KaisLissera/IR-motion-sensor/Doc/МГТУ.469335.001 Узел печатный.pdf

Формат
Кол.
А3 | | МГТУ.469335.001 СБ | Сборочный чертёж
А2 | | МГТУ.469335.001 Э3 | Схема электрическая
| | | | | принципиальная
| А4 | | | МГТУ.469335.001 ПЭ3 | Перечень элементов
| * | | | МГТУ.758741.001 ДЗЗ | Данные проектирования | *)CD
А3 | 1
Изм. | Лист | № докум. | Подп. | Дата
| | Разраб. | | | Спецификация | Лит. | Лист | Листов
Пров. | | | | | | | | 5

# МГТУ.469335.001

Подп. и дата Взам. инв. №

Инв. № подл.
МГТУ им Н.Э. Баумана
кафедра РЛ1

Н. контр.
Утв. | Круглов

### 1 Узел печатный

Краснинский Поз.

Инв. № дубл. Подп. дата

Документация

Детали

Плата печатная

МГТУ.758741.001

| Конденсаторы
2 | 04025U1CAT2A | 1 | С21*
| 1пФ+-0,25пФ 50В NP0
3 | 04025U5R6CAT2A | 1 | С20*
| | | 5,6пФ+-0,25пФ 50В NP0
| 4 | | 06032U18CAT2A | 4 | С23-С26
| | | 18пФ+-0,25пФ 200В NP0
| | | AVX Corporation
| 5 | | К10-90-1608-50В-100пФ+-5%-МП0 | 1 | С19
| 6 | | К10-90-1608-10В-100нФ+-10%-Н30 | 13 | C1-C5,C8-C15
| 7 | | К10-90-1608-10В-10мкФ+-10%-Н30 3 | | C16-C18
| | | ШУКР.673511.002 ТУ

Зона
Обозначение

Наименование

1

Примечание

Прочие изделия

Перв. примен.

МГТУ.464415.001

Справ. №

Копировал
Формат А4

| Микросхемы
8 | MCP1700T-3300E/TT | 1 | DA1
| Microchip Technology
9 | STM32F072RBT6 | 1 | DD1
| STMicroelectronics
| Предохранители
10 | MF-MSMF050 0,5А, Bourns | 1 | F1
| Приборы звуковой
| сигнализации
11 | HC0905A, JL World | 1 | HA1
| Индуктивности
13 | КИК 1005-1,2 нГн +-5% О-Л | 1 | L1*
| РКМУ.671340.002 ТУ
14 | BLM18AG102SN1D, Murata | 2 | L2,L3
| Резисторы
15 | Р1-8В-0,1-1 кОм+-10% Л-П-М | 6 | R9-R14
16 | Р1-8В-0,1-5,1 кОм+-10% Л-П-М | 2 | R1,R2
17 | Р1-8В-0,1-10 кОм+-10% Л-П-М | 1 | R3
18 | Р1-8В-0,1-100 кОм+-10% Л-П-М | 2 | R6,R7
| ОЖО.467.164 ТУ
Подп. | Дата

Приме-

Лист

# МГТУ.469335.001 2

№ докум.

Обозначение

| Светодиоды
12 | SMD05050C6 | 1 | HL1

Поз.

Инв. № подл.

Изм. Лист

Подп. и дата Взам. инв. № Инв. № дубл. Подп. дата

| Выключатели кнопочные
19 | KLS7-P8.5x8.5-1 | 1 | SB1
| Модуляторы
20 | RFM95W 868МГц, Hope RF | 1 | U1
| Диоды
21 | BAT760, NXP | 1 | VD2
22 | USBLC6-2SC6, STMicroelectronics | 1 | VD1
| Транзисторы
23 | SI2302A, UMW | 2 | VT1, VT3
| Резонаторы кварцевые
29 | 12MHz SMD03225C4 | 1 | ZQ1
30 | 32.768kHz SMD03215C2 | 1 | ZQ2
Переменные данные | для исполнений
| МГТУ.464415.001-00

Прочие изделия

| Резисторы
31 | Р1-8В-0,1-0 Ом+-10% Л-П-М | 1 | R17
Обозначение | Приме-
| Разъёмы
24 | PLS-2R тип D, Connfly | 1 | XP1
25 | PLS-6R тип D, Connfly | 1 | XP2
26 | USB Type-C 213716-0001, Ruichi | 1 | XS1

Инв. № дубл.

Подп. дата

Инв. № подл.

Лист | № докум.

Взам. инв. №

Подп. и дата

МГТУ.469335.001 | Лист 3 Изм.

Переменные данные | для исполнений
| МГТУ.464415.001-01

Прочие изделия

| Фотоэлементы
32 | SFH213FA, Osram | 1 | BL1
33 | TSOP4836, Vishay | 1 | BL2
| Конденсаторы
2 | 04025U1CAT2A 1пФ+-0,25пФ | 1 | C27*
| 50В NP0, AVX Corporation
34 | К10-90-1608-6,3В-680пФ+-10%-Н3 1 | | C22
6 | К10-90-1608-10В-100нФ+-10%-Н30 2 | | C6,C7
| ШУКР.673511.002 ТУ
| Микросхемы
35 | MCP6001RT-I/OT | 1 | DA1
| Microchip Technology

Резисторы
36 | Р1-8В-0,1-100 Ом+-10% Л-П-М | 1 | R4,R5
15 | Р1-8В-0,1-1 кОм+-10% Л-П-М | 1 | R8
18 | Р1-8В-0,1-100 кОм+-10% Л-П-М | 2 | R15
| ОЖО.467.164 ТУ
| Выключатели кнопочные
37 | KLS7-TS6601-5.0-180 | 1 | SB2
| KLS Electronics

Инв. № дубл. Подп. дата

Инв. № подл.

Взам. инв. №

Подп. и дата

МГТУ.469335.001 | Лист
Изм. | 4

| Диоды
38 | ESDA5V3L, STMicroelectronics | 1 | VD3

МГТУ.464415.001-02

Прочие изделия

| Резисторы
39 | Р1-8В-0,1-10 Ом+-10% Л-П-М | 1 | R16
| ОЖО.467.164 ТУ
| Выключатели кнопочные
37 | KLS7-TS6601-5.0-180 | 1 | SB2
| KLS Electronics
| Диоды
38 | ESDA5V3L, STMicroelectronics | 1 | VD3
40 | TSAL6200, Vishay | 1 | VD4
| Транзисторы
23 | SI2302A, UMV | 1 | VT2

Инв. № дубл. Подп. дата Инв. № подл.

Взам. инв. № Подп. и дата

# МГТУ.469335.001 Лист

5 Изм.
