KaisLissera/IR-motion-sensor/Doc/МГТУ.469335.001 Э3 Система электронного хронометража.pdf

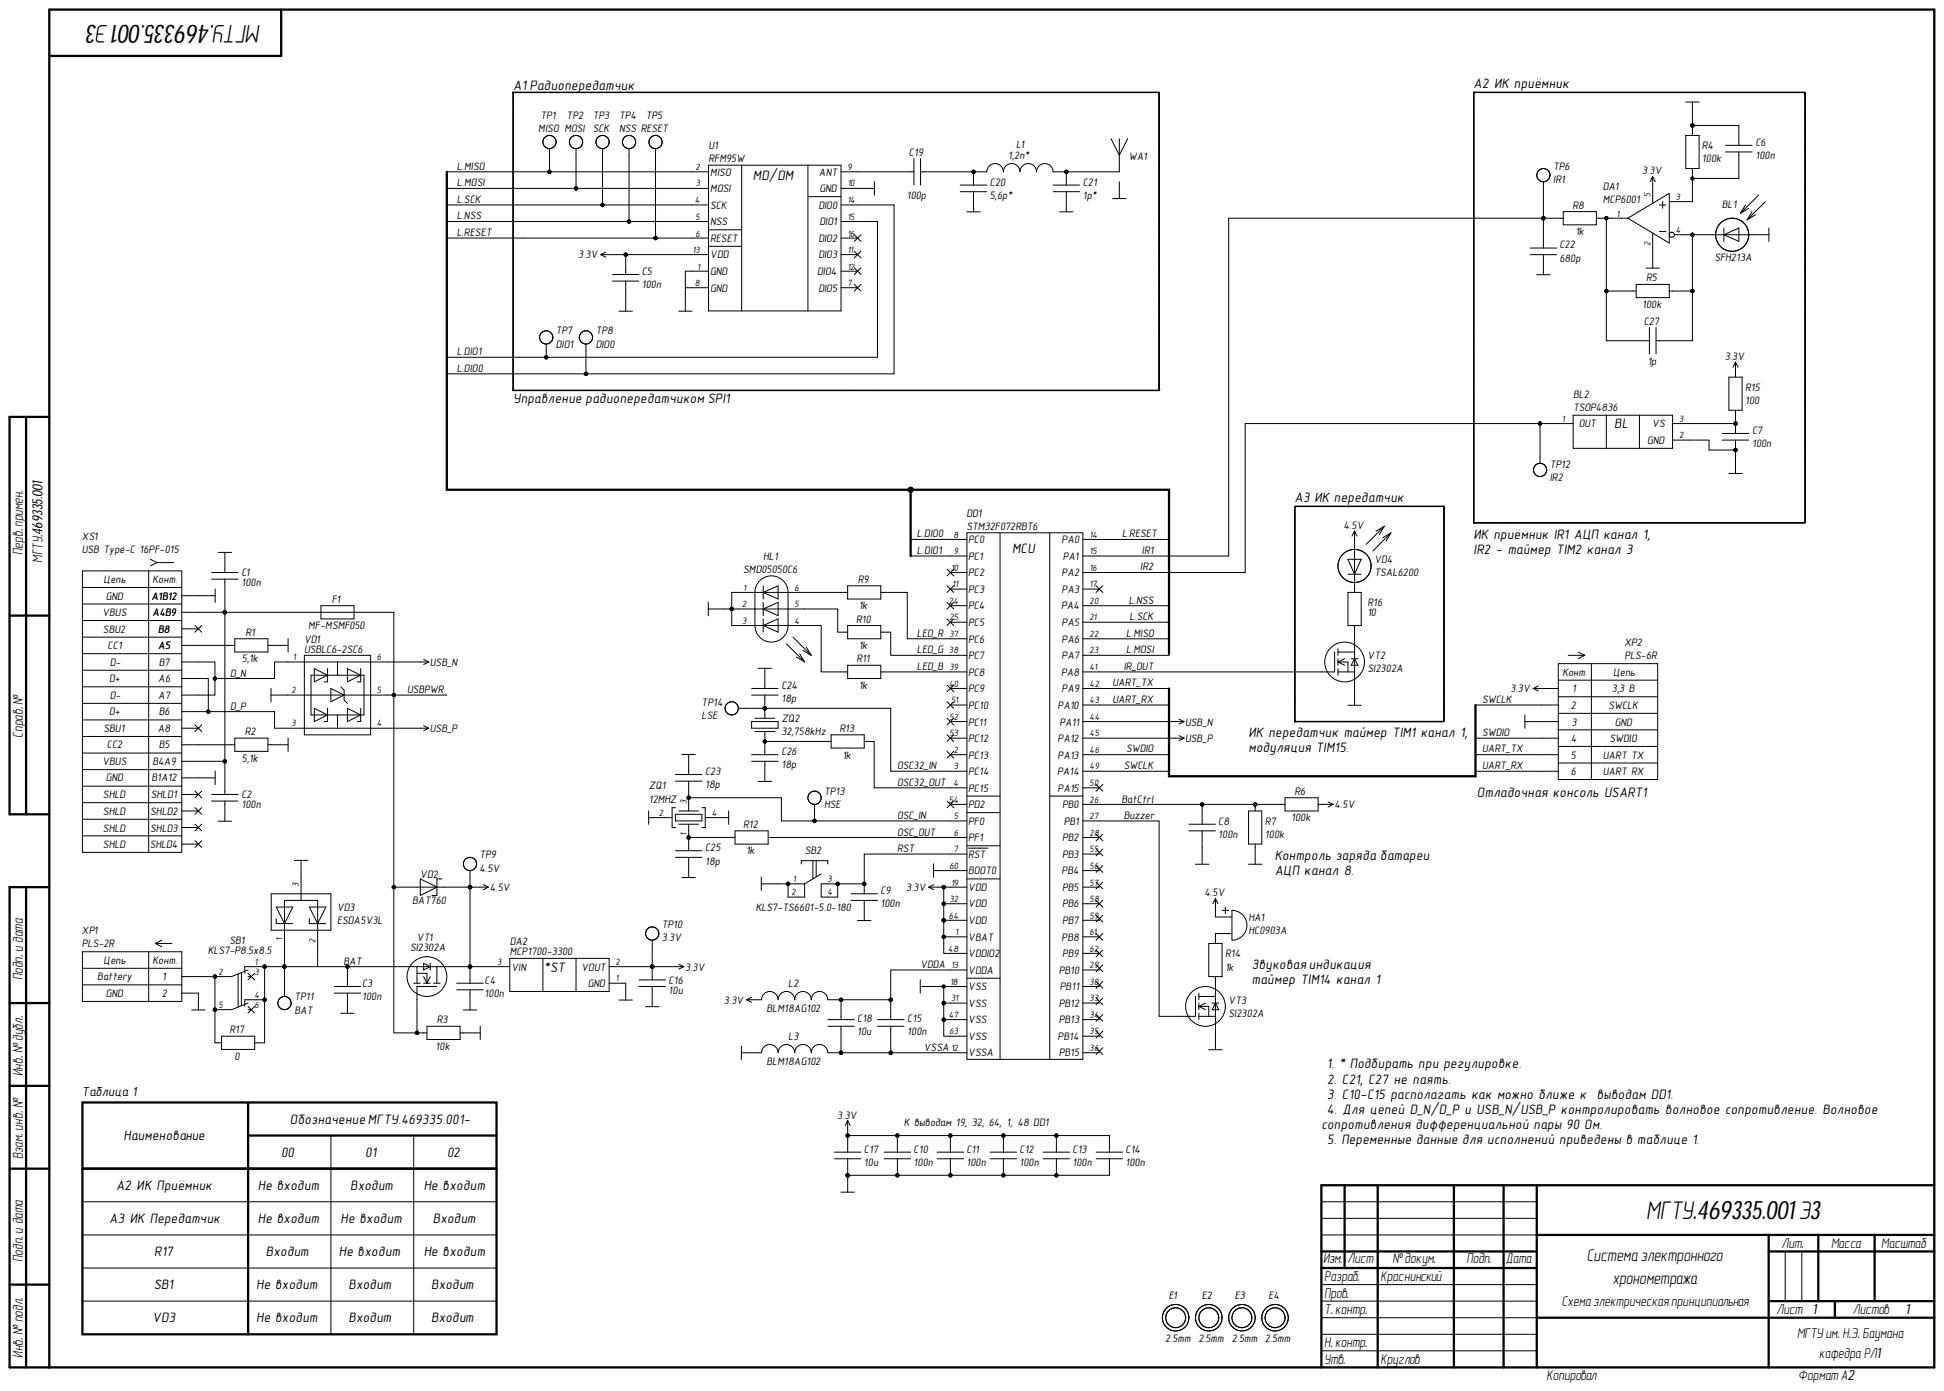
[picture p32: page 1]

L.MOSI | MOSI 3 | MD/DM

L.SCK | SCK 4

Инв. № подл. Подп. и дата Инв. №дубл. Подп. и дата Взам. инв. № Перв.примен. Справ. №

А3 ИК передатчик 4.5V

ИК приёмник IR1 АЦП канал 1,
IR2 - таймер TIM2 канал 3

ИК передатчик таймер TIM1 канал 1,
модуляция TIM15.

1. * Подбирать при регулировке.
2. C21, C27 не паять.
3. C10-C15 располагать как можно ближе к выводам DD1.
4. Для цепей D_N/D_P и USB_N/USB_P контролировать волновое сопротивление. Волновое
сопротивления дифференциальной пары 90 Ом.
5. Переменные данные для исполнений приведены в таблице 1.

Наименование | Обозначение МГТУ.469335.001-

А2 ИК Приёмник | Не входит | Входит | Не входит

МГТУ.469335.001 Э3

А3 ИК Передатчик | Не входит | Не входит | Входит

Н.контр.
Утв. | Круглов

МГТУ им. Н.Э. Баумана кафедра РЛ1
