KaisLissera/IR-motion-sensor/Bagryanets_hw/Photodiod_Amplifier.cir

[Main]
FileType=CIR
Version=12.00
Program=Micro-Cap
Component Version=10.00
Shape Version=11.00
Screen=1920,1080
MCAPVersion=12.2.0.5
Key ID=Demo
NLCnt=48
TXCnt=10

[shapedef]
Name=Battery
Line=0,0,22,0
Line=22,-3,22,3
Line=26,-7,26,7
Line=26,0,48,0
Current=32,8,16,8

[shapedef]
Name=Capacitor
Line=0,0,22,0
Line=22,-8,22,8
Line=26,-8,26,8
Line=26,0,48,0
Current=32,12,16,12

[shapedef]
Name=Diode.root
Line=0,0,20,0
Line=28,0,48,0
Rectangle=18,-8,20,8
PolyClosed=3
PolyLine=20,0
PolyLine=28,-8
PolyLine=28,8
Current=32,16,16,16

[shapedef]
Name=Ground
Line=0,0,12,0
Line=12,-8,12,8
Line=18,-4,18,4
Line=24,0,24,0

[shapedef]
Name=Minus.root
Line=-2,0,2,0

[shapedef]
Name=Opamp5
Root="Opamp.root",0,0,0
Root="Plus.root",25,-4,0
Root="Minus.root",25,52,0
Line=32,56,32,34
Line=32,-8,32,13

[shapedef]
Name=Opamp.root
Line=0,48,6,48
Line=0,0,5,0
Line=6,-4,6,52
Line=6,-4,48,24
Line=6,52,48,24
Line=48,24,72,24
Line=10,12,14,12
Line=12,10,12,14
Line=10,36,14,36
Line=4,0,6,0

[shapedef]
Name=Photodiode3
Root="Diode.root",0,48,0
Line=16,22,22,28
Line=10,28,16,34
PolyClosed=3
PolyLine=20,30
PolyLine=24,26
PolyLine=24,30
PolyClosed=3
PolyLine=14,36
PolyLine=18,32
PolyLine=18,36
Ellipse=-2,-2,2,2
FColor=None
Ellipse=46,-2,50,2
FColor=None
Line=8,6,8,10
Line=10,8,6,8

[shapedef]
Name=Plus.root
Line=-2,0,2,0
Line=0,-2,0,2

[shapedef]
Name=Pulse_Source
Root="Vsource.root",0,0,0
Line=20,-4,20,0
Line=20,0,26,0
Line=26,0,26,4

[shapedef]
Name=Resistor
PolyOpen=12
PolyLine=0,0
PolyLine=0,0
PolyLine=12,0
PolyLine=14,-4
PolyLine=18,4
PolyLine=22,-4
PolyLine=26,4
PolyLine=30,-4
PolyLine=34,4
PolyLine=36,0
PolyLine=48,0
PolyLine=48,0
Current=32,8,16,8

[shapedef]
Name=Vsource.root
Line=0,0,12,0
Line=36,0,48,0
Ellipse=12,-12,36,12
FColor=None
Line=7,5,7,9
Root="Plus.root",41,7,0
Current=32,16,16,16

[compdef]
Name=Battery
Definition=Battery
Shape=Battery
Mask=6145
Used=68
memo=Battery
Label Offset=19,7,10,13
PinCnt=2
Pin="Plus",6,0,-4,-5
Pin="Minus",0,0,-10,-5

[compdef]
Name=Ground
Definition=Ground
Shape=Ground
Mask=513
Used=296
memo=Ground
Label Offset=0,0,0,0
PinCnt=1
Pin="PinA",0,0,-3,-7

[compdef]
Name=Resistor
Definition=Resistor
Shape=Resistor
Mask=6145
Used=186
memo=Resistor
Label Offset=18,6,8,11
PinCnt=2
Pin="Plus",6,0,-10,-4
Pin="Minus",0,0,-14,-4

[compdef]
Name=Pulse Source
Definition=Pulse source
Shape=Pulse_Source
Mask=4864
Used=8
memo=Pulse Source
Label Offset=18,13,15,9
PinCnt=2
Pin="Plus",6,0,-5,-4
Pin="Minus",0,0,-19,-4

[compdef]
Name=SFH213
Definition=Subckt
Shape=Photodiode3
Mask=4224
Used=1
memo=PIN Photodiode Vr=20V Ip=135uA Id=1nA
Link=http://catalog.osram-os.com/catalogue/catalogue.do?act=downloadFile&favOid=020000030000b9ee000100b6
Label Offset=16,58,-19,10
PinCnt=4
Pin="OPT_IN+",a,0,0,-22,-4
Pin="OPT_IN-",a,6,0,-22,-4
Pin="CATH",a,0,6,-16,19
Pin="ANO",a,6,6,-7,19
Power=0.15

[compdef]
Name=Capacitor
Definition=Capacitor
Shape=Capacitor
Mask=7425
Used=28
memo=Capacitor
Label Offset=16,12,12,12
PinCnt=2
Pin="Plus",6,0,-3,-5
Pin="Minus",0,0,-14,-5

[compdef]
Name=LMC6001_NS
Definition=Subckt
Shape=Opamp5
Mask=4224
Used=2
memo=Precision CMOS Single Opamp
Label Offset=51,34,-8,44
PinCnt=5
Pin="1",a,0,0,-3,-4
Pin="2",a,0,6,-3,18
Pin="99",a,4,-1,6,15
Pin="50",a,4,7,6,0
Pin="28",a,9,3,-3,-3

[Circuit]
Window Placement=2,3, -1,-1, -8,-31, 0,0,1203,474
Default Object=Color=#000080
Default Object Font=Height=-15,FStyle=0,Color=#000080,Name=Arial
Default Object Apply Border To Text=No
Default Object Apply Fill To Text=No
Default Object GridSnap=No
NodeVoltageFormat=3
CurrentFormat=3
PowerFormat=3
PathDelayFormat=3
WarningFormat=3
GridTextFormulaFormat=3
Window Placement in Transient Analysis=0,1, -1,-1, -8,-31, 0,0,953,824
SpiceType=AMBIGUOUS
Title_Block_Border=None
Title_Block=False
Show Nodes=False
Show Voltages=False
Show Current=False
Show Power=False
Show Condition=False
Show Pin Connections=False
Show Connection Warnings=False
Show Cross=False
Show Attribute Text=True
Show Grid Text=True

[Comp]
Name=Battery
Px=48,80
Rot=3
Page=3

[Attr]
ON=-26,-41,PART
V=V1
Style=8192

[Attr]
ON=-26,-27,VALUE
V=3.3
Style=8192

[Comp]
Name=Ground
Px=48,80
Rot=7
Page=3

[Comp]
Name=Battery
Px=112,80
Rot=3
Page=3

[Attr]
ON=-26,-41,PART
V=V2
Style=8192

[Attr]
ON=-31,-27,VALUE
V=0
Style=8192

[Comp]
Name=Ground
Px=112,80
Rot=7
Page=3

[Wire]
Pxs=472,264,480,264
Color=#000000

[Comp]
Name=Ground
Color=#000000
FColor=#000000
Px=176,288
Rot=2

[Wire]
Pxs=544,264,584,264
Color=#000000

[Comp]
Name=Ground
Color=#000000
FColor=#000000
Px=392,136
Rot=3

[Comp]
Name=Resistor
Color=#000000
FColor=#000000
Px=456,328
Rot=2

[Attr]
ON=-30,7,PART
V=R4
Style=8192
Color=#000000

[Attr]
ON=-35,20,RESISTANCE
V=100k
Style=8192
Color=#000000

[Attr]
ON=0,22,FREQ
V
Color=#000000

[Attr]
ON=0,33,MODEL
V
Color=#000000

[Attr]
ON=0,44,SMOKE
V
Color=#000000

[Attr]
ON=0,55,FSV
V
Color=#000000

[Attr]
ON=0,66,COST
V
Color=#000000

[Attr]
ON=0,77,POWER
V
Color=#000000

[Attr]
ON=0,0,PACKAGE
V
Color=#000000

[Wire]
Pxs=392,200,392,208
Color=#000000

[Wire]
Pxs=392,240,400,240
Color=#000000

[Wire]
Pxs=392,136,392,144
Color=#000000

[Wire]
Pxs=392,288,392,328
Color=#000000

[Wire]
Pxs=392,328,408,328
Color=#000000

[Wire]
Pxs=392,288,400,288
Color=#000000

[Wire]
Pxs=456,328,480,328
Color=#000000

[Wire]
Pxs=480,264,480,328
Color=#000000

[Wire]
Pxs=480,264,544,264
Color=#000000

[Wire]
Pxs=176,288,192,288
Color=#000000

[Comp]
Name=Pulse Source
Color=#000000
FColor=#000000
Px=192,224

[Attr]
ON=18,-28,PART
V=V3
Style=8192
Color=#000000

[Attr]
ON=-70,-37,MODEL
V=IMPULSE
Color=#000000

[Attr]
ON=0,22,SMOKE
V
Color=#000000

[Attr]
ON=0,33,COST
V
Color=#000000

[Attr]
ON=0,44,POWER
V
Color=#000000

[Attr]
ON=0,0,PACKAGE
V
Color=#000000

[Comp]
Name=SFH213
Color=#000000
FColor=#000000
Px=240,240
Rot=6

[Attr]
ON=-31,58,PART
V=X6
Style=8192
Color=#000000

[Attr]
ON=-42,72,NAME
V=SFH213
Style=8192
Color=#000000

[Attr]
ON=0,22,FILE
V
Color=#000000

[Attr]
ON=0,33,PARAMS:
V
Color=#000000

[Attr]
ON=0,44,OPTIONAL:
V
Color=#000000

[Attr]
ON=0,55,TEXT:
V
Color=#000000

[Attr]
ON=0,66,COST
V
Color=#000000

[Attr]
ON=-16,86,POWER
V=0.15
Color=#000000

[Attr]
ON=0,0,PACKAGE
V
Color=#000000

[Wire]
Pxs=240,224,240,240
Color=#000000

[Wire]
Pxs=192,224,192,240
Color=#000000

[Comp]
Name=Ground
Color=#000000
FColor=#000000
Px=176,224
Rot=2

[Wire]
Pxs=176,224,192,224
Color=#000000

[Wire]
Pxs=240,288,392,288
Color=#000000

[Comp]
Name=Capacitor
Color=#000000
FColor=#000000
Px=408,384

[Attr]
ON=16,12,PART
V=C2
Style=8192
Color=#000000

[Attr]
ON=16,26,CAPACITANCE
V=8p
Style=8192
Color=#000000

[Attr]
ON=0,22,CHARGE
V
Color=#000000

[Attr]
ON=0,33,FREQ
V
Color=#000000

[Attr]
ON=0,44,MODEL
V
Color=#000000

[Attr]
ON=0,55,SMOKE
V
Color=#000000

[Attr]
ON=0,66,FSV
V
Color=#000000

[Attr]
ON=0,77,COST
V
Color=#000000

[Attr]
ON=0,88,POWER
V
Color=#000000

[Attr]
ON=0,0,PACKAGE
V
Color=#000000

[Wire]
Pxs=392,328,392,384
Color=#000000

[Wire]
Pxs=392,384,408,384
Color=#000000

[Wire]
Pxs=456,384,480,384
Color=#000000

[Wire]
Pxs=480,328,480,384
Color=#000000

[Comp]
Name=Resistor
Color=#000000
FColor=#000000
Px=584,264

[Attr]
ON=15,9,PART
V=R5
Style=8192
Color=#000000

[Attr]
ON=17,25,RESISTANCE
V=1k
Style=8192
Color=#000000

[Attr]
ON=0,22,FREQ
V
Color=#000000

[Attr]
ON=0,33,MODEL
V
Color=#000000

[Attr]
ON=0,44,SMOKE
V
Color=#000000

[Attr]
ON=0,55,FSV
V
Color=#000000

[Attr]
ON=0,66,COST
V
Color=#000000

[Attr]
ON=0,77,POWER
V
Color=#000000

[Attr]
ON=0,0,PACKAGE
V
Color=#000000

[Comp]
Name=Capacitor
Color=#000000
FColor=#000000
Px=648,280
Rot=1

[Attr]
ON=12,12,PART
V=C3
Style=8192
Color=#000000

[Attr]
ON=14,26,CAPACITANCE
V=1.6n
Style=8192
Color=#000000

[Attr]
ON=0,22,CHARGE
V
Color=#000000

[Attr]
ON=0,33,FREQ
V
Color=#000000

[Attr]
ON=0,44,MODEL
V
Color=#000000

[Attr]
ON=0,55,SMOKE
V
Color=#000000

[Attr]
ON=0,66,FSV
V
Color=#000000

[Attr]
ON=0,77,COST
V
Color=#000000

[Attr]
ON=0,88,POWER
V
Color=#000000

[Attr]
ON=0,0,PACKAGE
V
Color=#000000

[Comp]
Name=Ground
Color=#000000
FColor=#000000
Px=648,344
Rot=1

[Wire]
Pxs=632,264,648,264
Color=#000000

[Wire]
Pxs=648,264,648,280
Color=#000000

[Wire]
Pxs=648,328,648,344
Color=#000000

[Wire]
Pxs=648,264,656,264
Color=#000000

[Comp]
Name=Resistor
Color=#000000
FColor=#000000
Px=392,152
Rot=1

[Attr]
ON=-24,9,PART
V=R6
Style=8192
Color=#000000

[Attr]
ON=-32,22,RESISTANCE
V=100k
Style=8192
Color=#000000

[Attr]
ON=0,22,FREQ
V
Color=#000000

[Attr]
ON=0,33,MODEL
V
Color=#000000

[Attr]
ON=0,44,SMOKE
V
Color=#000000

[Attr]
ON=0,55,FSV
V
Color=#000000

[Attr]
ON=0,66,COST
V
Color=#000000

[Attr]
ON=0,77,POWER
V
Color=#000000

[Attr]
ON=0,0,PACKAGE
V
Color=#000000

[Comp]
Name=Capacitor
Color=#000000
FColor=#000000
Px=344,200
Rot=3

[Attr]
ON=-27,-39,PART
V=C4
Style=8192
Color=#000000

[Attr]
ON=-37,-25,CAPACITANCE
V=100n
Style=8192
Color=#000000

[Attr]
ON=0,22,CHARGE
V
Color=#000000

[Attr]
ON=0,33,FREQ
V
Color=#000000

[Attr]
ON=0,44,MODEL
V
Color=#000000

[Attr]
ON=0,55,SMOKE
V
Color=#000000

[Attr]
ON=0,66,FSV
V
Color=#000000

[Attr]
ON=0,77,COST
V
Color=#000000

[Attr]
ON=0,88,POWER
V
Color=#000000

[Attr]
ON=0,0,PACKAGE
V
Color=#000000

[Wire]
Pxs=344,144,344,152
Color=#000000

[Wire]
Pxs=344,144,392,144
Color=#000000

[Wire]
Pxs=392,144,392,152
Color=#000000

[Wire]
Pxs=344,200,344,208
Color=#000000

[Wire]
Pxs=344,208,392,208
Color=#000000

[Wire]
Pxs=392,208,392,240
Color=#000000

[Comp]
Name=LMC6001_NS
Color=#000000
FColor=#000000
Px=400,240

[Attr]
ON=53,-6,PART
V=X7
Style=8192
Color=#000000

[Attr]
ON=52,6,NAME
V=LMC6001_NS
Style=8192
Color=#000000

[Attr]
ON=0,22,FILE
V
Color=#000000

[Attr]
ON=0,33,PARAMS:
V
Color=#000000

[Attr]
ON=0,44,OPTIONAL:
V
Color=#000000

[Attr]
ON=0,55,TEXT:
V
Color=#000000

[Attr]
ON=0,66,COST
V
Color=#000000

[Attr]
ON=0,77,POWER
V
Color=#000000

[Attr]
ON=51,76,PACKAGE
V=DIP8
Color=#000000

[Wire]
Pxs=656,264,672,264
Color=#000000

[Grid Text]
Text=".DEFINE L 150u"
Px=456,168
Color=#000000
GridSnap=True
JustifyH=Left
JustifyV=Bottom
CBorder=None

[Grid Text]
Text="OUT"
Px=544,264
Color=#000000
GridSnap=True
JustifyH=Left
JustifyV=Bottom
CBorder=None

[Grid Text]
Text="VC"
Px=48,32
GridSnap=True
JustifyH=Left
JustifyV=Bottom
Page=3
CBorder=None

[Grid Text]
Text="VC"
Px=432,232
Color=#000000
GridSnap=True
JustifyH=Left
JustifyV=Bottom
CBorder=None

[Grid Text]
Text="VE"
Px=112,32
GridSnap=True
JustifyH=Left
JustifyV=Bottom
Page=3
CBorder=None

[Grid Text]
Text="VE"
Px=432,296
Color=#000000
GridSnap=True
JustifyH=Left
JustifyV=Bottom
CBorder=None

[Grid Text]
Text="imp"
Px=240,224
Color=#000000
GridSnap=True
JustifyH=Left
JustifyV=Bottom
CBorder=None

[Grid Text]
Text=".DEFINE Noise 0"
Px=456,184
Color=#000000
GridSnap=True
JustifyH=Left
JustifyV=Bottom
CBorder=None

[Grid Text]
Text="ADC"
Px=656,264
Color=#000000
GridSnap=True
JustifyH=Left
JustifyV=Bottom
CBorder=None

[Grid Text]
Text=".DEFINE DutyCycle 0.5"
Px=456,200
Color=#000000
GridSnap=True
JustifyH=Left
JustifyV=Bottom
CBorder=None

[Schematic]
CurrentSection 0=0
CurrentSection 1=0
CurrentSection 2=0
CurrentSection 3=0
Splitter.xs=0
Splitter.ys=0
TextQuad=4099
Scale=1
GridUser=10
ShapeGroups="Main","Euro","Polarity","Main1","Main11","Electrolytic","GroundArrow","DeMorgan"
CalcRMS=False
CalcAVG=False
CalcPeak=False
CalcVoltage=True
DisplayMeasure=Last
ShareScales=True

[Tools]
Pos=Top
FILESAVEASOLD=No
BOM=No
FILEPCB=No
PROBE=Yes
SELECT=Yes
PAN=Yes
COMP=Yes
TEXT=Yes
WIRE=Yes
WIRED=Yes
BUS=Yes
GRAPHIC=Yes
FLOWCHART=Yes
LINE=No
ELLIPSE=No
RECT=No
DIAM=No
ARC=No
PIE=No
TRIANGLE=No
STAR=No
LEFTBRK=No
RIGHTBRK=No
BOTHBRK=No
META=Yes
PARALLELOGRAM=No
FC_PROCESS=No
FC_ALT_PROCESS=No
FC_DECISION=No
FC_DATA=No
FC_PREDEFPROCESS=No
FC_INTERNALSTORAGE=No
FC_DOCUMENT=No
FC_MULTIDOCUMENT=No
FC_TERMINATOR=No
FC_PREPARATION=No
FC_MANUALINPUT=No
FC_MANUALOPERATION=No
FC_CONNECTOR=No
FC_OFFPAGECONNECTOR=No
FC_PUNCHCARD=No
FC_PUNCHEDTAPE=No
FC_SUMMING_JUNCTION=No
FC_OR=No
FC_COLLATE=No
FC_SORT=No
FC_EXTRACT=No
FC_MERGE=No
FC_STORED_DATA=No
FC_DELAY=No
FC_SAS=No
FC_MAGNETIC_DISK=No
FC_DAS=No
FC_DISPLAY=No
SPREAD_SHEET=Yes
POLYCLOS=No
POLYOPEN=No
FLAG=Yes
INFO=Yes
HELP=Yes
HELP_SPICE=No
LINK=Yes
CHECK=Yes
REGION_ENABLE=Yes
TITLE_BLOCK=Yes
DIGTRC=No
DIGTRC2=No
BUILD_COMMAND=Yes
DIGALL=No
GRIDTEXT=Yes
COMPTEXT=Yes
NODE=Yes
MEASURED=Yes
NODEV=Yes
CURRENT=Yes
POWER=Yes
CONDITIN=Yes
PIN=Yes
CONNWARN=Yes
CROSS=Yes
GRID=Yes
BORDER=Yes
BORDERONE=Yes
TITLE=Yes
RUBBER=Yes
PROPERTY=Yes
STEP=Yes
MIRROR=Yes
ROTATE=Yes
FLIPY=Yes
FLIPX=Yes
CIR_MAKEMACRO=No
CLEARCUTWIRE=No
CLIPBOARDCIRPAGE2BMM=No
FINDCOMP=Yes
FIND=Yes
REPEAT=No
REPLACE=No
MODEL=Yes
CIR2CKT=Yes
ATTDISP=Yes
ENABLE=Yes
DISABLE=Yes
ENABLE_WITH=Yes
TOFRONT=Yes
TOBACK=Yes
SELNEXT=Yes
PAGEADD=Yes
PAGEADDTEXT=No
ADDSECTION=No
PAGEDEL=Yes
ZOOMIN=Yes
ZOOMOUT=Yes
AUTOSCALECIR=Yes
GOTOFLAG=Yes
UPLEVEL=Yes
COLOR=Yes
FONT=Yes
STYLE=Yes
DM_LAST=No
DM_RMS=No
DM_AVG=No
DM_PEAK=No
GRID_NONE=No
GRID_NORMAL=No
GRID_BOLD_5=No
GRID_BOLD_6=No
GRID_BOLD_USER=No
GRAPH_PAPER=No
SPLITCIRTEXTH=No
SPLITCIRTEXTV=No
SPACE_SPLITTERS_EVENLY=No
NORMALCIR=No
RENAMEDEFINE=No
RENAMECMP=No
ATTALIGN=No
RESETNODEPOS=No
FIT2STANDARD=No
NODESNAP=No
MOVETEXT=No
TEXTINC=No
TOGGLETEXT=No
TOGGLEMODE=No
TOLERANCE=No
ALIGNAB=No
ALIGNLEFT=Yes
ALIGNCENTER=Yes
ALIGNRIGHT=Yes
ALIGNTOP=Yes
ALIGNMIDDLES=Yes
ALIGNBOTTOM=Yes

[Section]
Index=0
Name="Photodiod_Amplifier"
Type=Main
Enable=True
CurrentPage 0=0
CurrentPage 1=0
CurrentPage 2=0
CurrentPage 3=0
TabSize 0=425
TabSize 1=425
TabSize 2=425
TabSize 3=425

[Page]
Index=0
Section=0
Print=True
Enable=True
Name=Main
PrinterScale=1
Scale 0=1
Scale 1=1
Scale 2=1
SB 3=101,73
Scale 3=0.66666666666666663
Px=214,228
WinBackGround Color=#FFFFFF
Select Color=#FF0000
Anchor Color=#000000
Select Box Color=#000080
Grid Text Color=Height=-12,FStyle=0,Color=#0000FF,Name=Verdana
Grid Text RTF=False
Grid Text Angle=0
Grid Text GridSnap=True
Grid Text PinIt=False
Grid Text JustifyH=Left
Grid Text JustifyV=Bottom
Grid GradientColor2=None
Grid OutlineThickness=1
Grid OutlineColor=None
Component Color=#0000FF
Attribute Text=Height=-12,FStyle=0,Color=#008000,Name=Verdana
Wire Color=#008000
Bus Color=#008000
Pin Connection=Height=-10,FStyle=0,Color=#FF0000,Name=Arial
Pin Marker Color=#008000
Node Number=Height=-11,FStyle=0,Color=#FF00FF,Name=Arial
Node Voltage Color=Height=-11,FStyle=0,Color=#000000,Name=Arial
Dynamic AC Voltage Color=#E4E4E4
Text Banner Text=Height=-15,FStyle=0,Color=#800000,Name=Arial
Title Block Background=#C0C0C0
Current=Height=-11,FStyle=0,Color=#0000FF,Name=Arial
Power/Condition=Height=-11,FStyle=0,Color=#FF0000,Name=Arial
Digital Path Color=#FF0000
Title Block Border=#000000
Disabled	Color=#C0C0C0
Search Color=#FFFF00
Grid Color=#000000
Graph Paper=#E4E4E4
Digital 0 Color=#000000
Digital R Color=#FFFF00
Digital F Color=#FFFF00
Digital 1 Color=#FF0000
Digital X Color=#C0C0C0
Digital Z Color=#808080
Block Select Color=#51F998

[Page]
Index=1
Section=0
Type=Text
Print=False
Enable=True
Name=Text
Font=Height=-15,FStyle=0,Color=#000000,Name=Courier New
Comment Color=#008000
WinBackGround Color=#FFFFFF
Disabled	Color=#C0C0C0
KeyWord Color=#0000FF
Error	Color=#FF0000
Search Color=#FFFF00

[Page]
Index=2
Section=0
Type=Text
Print=False
Enable=True
Name=Models
SB 0=39,25
Font=Height=-15,FStyle=0,Color=#000000,Name=Courier New
Comment Color=#008000
WinBackGround Color=#FFFFFF
Disabled	Color=#C0C0C0
KeyWord Color=#0000FF
Error	Color=#FF0000
Search Color=#FFFF00

[Page]
Index=3
Section=0
Print=True
Enable=True
Name=Power Supplies
PrinterScale=1
Scale 0=1
Scale 1=1
Scale 2=1
Scale 3=1
Px=120,55
WinBackGround Color=#FFFFFF
Select Color=#FF0000
Anchor Color=#000000
Select Box Color=#000080
Grid Text Color=Height=-12,FStyle=0,Color=#0000FF,Name=Verdana
Grid Text RTF=False
Grid Text Angle=0
Grid Text GridSnap=True
Grid Text PinIt=False
Grid Text JustifyH=Left
Grid Text JustifyV=Bottom
Grid GradientColor2=None
Grid OutlineThickness=1
Grid OutlineColor=None
Component Color=#0000FF
Attribute Text=Height=-12,FStyle=0,Color=#008000,Name=Verdana
Wire Color=#008000
Bus Color=#008000
Pin Connection=Height=-10,FStyle=0,Color=#FF0000,Name=Arial
Pin Marker Color=#008000
Node Number=Height=-11,FStyle=0,Color=#FF00FF,Name=Arial
Node Voltage Color=Height=-11,FStyle=0,Color=#000000,Name=Arial
Dynamic AC Voltage Color=#E4E4E4
Text Banner Text=Height=-15,FStyle=0,Color=#800000,Name=Arial
Title Block Background=#C0C0C0
Current=Height=-11,FStyle=0,Color=#0000FF,Name=Arial
Power/Condition=Height=-11,FStyle=0,Color=#FF0000,Name=Arial
Digital Path Color=#FF0000
Title Block Border=#000000
Disabled	Color=#C0C0C0
Search Color=#FFFF00
Grid Color=#000000
Graph Paper=#E4E4E4
Digital 0 Color=#000000
Digital R Color=#FFFF00
Digital F Color=#FFFF00
Digital 1 Color=#FF0000
Digital X Color=#C0C0C0
Digital Z Color=#808080
Block Select Color=#51F998

[Page]
Index=4
Section=0
Type=Info
Print=False
Enable=True
Name=Info
Font=Height=-15,FStyle=0,Color=#000000,Name=Courier New
Comment Color=#008000
WinBackGround Color=#FFFFFF
Disabled	Color=#C0C0C0
KeyWord Color=#0000FF
Error	Color=#FF0000
Search Color=#FFFF00

[Text Area]
Section=0
Page=1
Text=.OPTIONS ITL4=50

[Text Area]
Section=0
Page=2
Text=* Schematic File
Text=*
Text=* Syntax:
Text=* .MODEL <model name> [AKO:<reference model name>] <ModelType>
Text=* +([<parameter name>=<value>][LOT[/#][/GAUSS|/UNIFORM|/WCASE]=[<tol>[%]] |[-<low>%,<high>%]][DEV[/#][/GAUSS|/UNIFORM|/WCASE]=[<tol>[%]]...)
Text=* ModelType must be one of OPA,D,NPN,NMOS,NJF,PUL,SIN,TRN,CORE,GASFET,VSWITCH,ISWITCH,CAP,IND,RES,PNP,PMOS,PJF,DOUTPUT,DINPUT,UADC,UDAC,UGATE,UTGATE,UEFF,UGFF,UDLY,UPLD,UROM,URAM,UBGT,UIO,LPNP,NIGBT,I,V
Text=*
Text=*Examples:
Text=* .MODEL 2N2222A NPN(BF=150 IS=1E-14)
Text=* .model M1 NMOS(KP=2.5E-5 VTO=1.345 CGDO=14.67p CGBO=4.566p)
Text=* .MODEL DK D(IS=1E-18)
Text=* .model 2N2222A AKO:2N2222 NPN (BF=55 ISE=10F)
Text=* .Model BJT1 NPN (RE=12 LOT/1/GAUSS=30% DEV/2/UNIFORM=2%)
Text=*
Text=* A .cir file is typically found in the data directory
Text=*
Text=*** From file C:\MC12\library\UTILITY.LBR
Text=*** 1MHz Sinusoidal Source
Text=.MODEL 1MHZ SIN (A=5 F=200k)
Text=*** From file C:\MC12\library\UTILITY.LBR
Text=*** 60HZ Sinusoidal Source
Text=.MODEL 60HZ SIN (A=0 F=10MEG)
Text=*** From file C:\MC12\library\UTILITY.LBR
Text=*** 1ns Impulse Source
Text=.MODEL IMPULSE PUL (P1={30u*(1 - DutyCycle)} P2={30u*(1 - DutyCycle)} P3=30u
Text=+ P4=30u P5=30u VONE={L} VZERO={Noise})

[InfoPage]
InfoPage=True
Warnings=True
System=True
Defines=True
Array=True
Model=True
Measure=True
MacroSubckt=True
NotUsed=True
ComponentCounts=True
VariablizePaths=False
DontShowPaths=False
SimulationLog=True

[Transient]
WinID=1
Window Placement=0,1, -1,-1, -8,-31, 953,0,1906,824
Font=Height=-19,FStyle=0,Color=#000000,Name=Arial
WinBackGround Color=#FFFFFF
Select Color=#FF0000
Anchor Color=#000000
Select Box Color=#000080
Title=Photodiod_Amplifier.cir
AutoTitle=Yes
Grid Color=#808080
Grid Weight=1
Grid Pattern=Dot6
Tracker Foreground=Height=-15,FStyle=0,Color=#000000,Name=Arial
Tracker Background=#FFFF00
Baseline color=#000000
BaseLine Weight=1
CurveFit color=#FF0000
CurveFit Weight=2
CurveFit Pattern=Dash
Static Grids=False
PlusMark=False
MinorLog25=Off
LabelMinor=Off
DataPoints=False
Token=False
Ruler=False
XAxisGrids=True
YAxisGrids=True
MinorLogGrids=True
BaseLine=False
AlignZ=True
Align Cursors=True
TagFormatX=3
TagFormatY=3
FormulaFormat=2
EndMode=SCALE
Graph Background=#FFFFFF
Tracker Intercept=False
Tracker Mouse=True
Tracker Cursor=True
Tracker Cursor BranchInfo=False
Horizontal Cursor=False
Same Y Scales=Yes
Enable X Scaling=True
Enable Y Scaling=True
Keep X Scales The Same=True
Number of Grids X=5
Number of Grids Y=5
Cursor Select Color Primary=#C0C0C0
Cursor Select Color Secondary=#FF0000
Data Point Labels Color Fore=Height=-15,FStyle=0,Color=#000000,Name=Arial
Data Point Labels Color Back=#FFFF00
OperPoint=False
OperPointOnly=False
AutoScaleRanges=False
FixedTimeStep=False
DoPSS=False
PSS_Periods="1"
PSS_Iterations="5"
PSS_Error="1u"
PSS_ShowPlots=True
FFT_NPts="8192"
FFT_IncludeDCHarmonic=False
FFT_AutoScale_Harmonics="10"
PrinterAutoTile=No
PrinterBlackBorder=No
MonMaxShow=4
MonPageWidth=66
MonPlotWidth=21
MonExprXWidth=142
MonExprYWidth=367
MonRangeXWidth=90
MonRangeYWidth=90
AnimateWait=None
AnimateWaitTime=500
AnimatePressAfter=0
Save_For_Future=No
Reduce_Display=1
Reduce_Save=1
Reduce_ThrowDataOut=0
Num Out Header Left
Num Out Header Center="$MC\n$user\n$company\n$Analysis of $name\n$date $time"
Num Out Header Right
Num Out Delimiter=32
Num Out Write=True
Num Out Write Main Header=True
Num Out Write Limits=True
Num Out Write Branch Header=True
Num Out Write Models=False
Num Out Write Zero Models=True
Num Out Write Undefined Models=True
Num Out Write Operating Point=True
Num Out Write Measurement Values=True
Num Out Write Tolerance Detail=True
Num Out Write Values=True
Num Out Write Waveform Header=True
Num Out Allow Dup Y Expr=False
Num Out Low="TSTART"
Num Out High="TMAX"
Num Out Font=Height=-15,FStyle=0,Color=#000000,Name=Courier New
Num Out Format=3
Num Out HideNonSelected=False
Num Out UseActualDataPoints=False
AutoSaveWave=False
Wave Format=16E
State Variables Format=5E
Print Individual Pages=False

[Tools]
Pos=Top
SELECT=Yes
PAN=Yes
GRAPHIC=Yes
LINE=No
ELLIPSE=No
RECT=No
DIAM=No
ARC=No
PIE=No
TRIANGLE=No
STAR=No
LEFTBRK=No
RIGHTBRK=No
BOTHBRK=No
META=Yes
PARALLELOGRAM=No
POLYCLOS=No
POLYOPEN=No
SCALE=Yes
CURSOR=Yes
MEASUREH=Yes
MEASUREV=Yes
TAG=Yes
PTAG=Yes
TEXT=Yes
PROPERTY=Yes
START=Yes
STOP=Yes
PAUSE=Yes
RESUME=No
DATAPTS=Yes
TOKENS=Yes
RULER=Yes
PLUS=Yes
XAXIS=Yes
YAXIS=Yes
MINORLOG=Yes
LOG25=Yes
BASELINE=Yes
HORIZCUR=Yes
GOTOX=Yes
GOTOY=Yes
GOTOPERF=Yes
GOTOBRNC=Yes
CLEAR_ACCUMULATED=Yes
PDELETE_ALL_PLOTS=Yes
NEXT=Yes
NEXTIN=Yes
PEAK=Yes
VALLEY=Yes
HIGH=Yes
LOW=Yes
INFLECTN=Yes
GHIGH=Yes
GLOW=Yes
BOTTOM=Yes
TOP=Yes
WAVEFORMBUFFER=Yes
AOUTPUT=Yes
PKEY=Yes
ENXSCALE=Yes
ENYSCALE=Yes
ZOOMIN=Yes
ZOOMOUT=Yes
AUTOSCALE=Yes
RESTORESCALE=No
COLOR=Yes
FONT=Yes
STYLE=Yes
SELNEXT=Yes
NORMALIZE=No
NORMALIZE_MIN=No
NORMALIZE_MAX=No
ADD_TAG_LEFT=No
ADD_TAG_RIGHT=No
ADD_HORZ_TAG=No
ADD_VERT_TAG=No
ALIGN_CURSORS=No
ALIGN_CURSORSZ=No
CURSORTOCLIPBOARD=No
TRACKER_CURSOR=No
TRACKER_CURSOR_BRANCHINFO=No
TRACKER_INTERCEPT=No
TRACKER_MOUSE=No
TOFRONT=Yes
TOBACK=Yes
SPLITCIRTEXTH=No
SPLITCIRTEXTV=No
SPACE_SPLITTERS_EVENLY=No
NORMALCIR=No
LABEL_WAVEFORM=No
LABEL_DATA_POINTS=No
WFB_ADD_TO_LIMITS=No
ENVELOPE=No
SAMEYSCALES=No
KEEPXSCALESTHESAME=No
CURVEFIT=No
ADD_MARKER=No
SHOWWATCH=No
BP=No
TOGGLEMODE=No
REMOVEALLTEXT=No
AUTOSCALEX=No
LABELALLMINOR=No
ALIGNLEFT=Yes
ALIGNCENTER=Yes
ALIGNRIGHT=Yes
ALIGNTOP=Yes
ALIGNMIDDLES=Yes
ALIGNBOTTOM=Yes

[APage]
Analysis=Transient
Name="MAIN"

[Monte Carlo Options]
Analysis=Transient
Status=Off
Zero Tolerance=False
Eliminate Outliers=False
Distribution=Normal
Number of Runs=10
Seed=0

[Limits]
Analysis=Transient
TMax=400u
TStart=300u
TStep=100n
NPts=1000
Temp=27
RetraceRuns=1
StateVar=Zero
RunOption=Normal
Temperature Type=Linear
Accumulate Plots=False
IgnoreExprErrors=False

[WaveForm]
Analysis=Transient
Plt=1
AliasID=1
XExp=T
YExp=i(X6.d1)
XRng=400u, 300u
YRng=AutoAlways
Options=LINEARX,LINEARY
Range Grid X=10u
Enable=DontRun
Line Color=#0000FF
Text Color=#0000FF
Rainbow=False
VFmtX=3
VFmtY=3
ScaleFactorX="None"
ScaleFactorY="None"
ScaleUnitsX="Auto"
ScaleUnitsY="Auto"
SFmtX=2
SFmtY=2
NOFmtX=3E
NOFmtY=3E

[WaveForm]
Analysis=Transient
Plt=2
AliasID=2
XExp=T
YExp=v(imp)
XRng=400u, 300u
YRng=AutoAlways
Options=LINEARX,LINEARY
Range Grid X=10u
Enable=Enable
CS=Normal
Line Color=#000000
Text Color=#000000
Rainbow=False
VFmtX=3
VFmtY=3
ScaleFactorX="None"
ScaleFactorY="None"
ScaleUnitsX="Auto"
ScaleUnitsY="Auto"
SFmtX=2
SFmtY=2
NOFmtX=3E
NOFmtY=3E

[WaveForm]
Analysis=Transient
Plt=3
AliasID=3
XExp=T
YExp=v(OUT)
XRng=400u, 300u
YRng=4,-1
Options=LINEARX,LINEARY
Range Grid X=10u
Range Grid Y=1
Enable=Enable
CS=Normal
Line Color=#000000
Text Color=#000000
Rainbow=False
VFmtX=3
VFmtY=3
ScaleFactorX="None"
ScaleFactorY="None"
ScaleUnitsX="Auto"
ScaleUnitsY="Auto"
SFmtX=2
SFmtY=2
NOFmtX=3E
NOFmtY=3E

[WaveForm]
Analysis=Transient
Plt=4
AliasID=4
XExp=T
YExp=v(ADC)
XRng=400u, 300u
YRng=4,-1
Options=LINEARX,LINEARY
Range Grid X=10u
Range Grid Y=1
Enable=Enable
CS=Normal
Line Color=#000000
Text Color=#000000
Rainbow=False
VFmtX=3
VFmtY=3
ScaleFactorX="None"
ScaleFactorY="None"
ScaleUnitsX="Auto"
ScaleUnitsY="Auto"
SFmtX=2
SFmtY=2
NOFmtX=3E
NOFmtY=3E

[Limits]
Analysis=DynamicAC
FirstValueDisplay=Mag
SecondValueDisplay=PhaseDeg
PlaceText=True

[Limits]
Analysis=DynamicDC
PlaceText=True

[Pane]
Analysis=Transient
CurrentPage 0="MAIN"

[Pane]
Analysis=AC

[Pane]
Analysis=DC

[Pane]
Analysis=HmDistortion

[Pane]
Analysis=ImDistortion

[Pane]
Analysis=Stability

[Watch]
Analysis=Transient
Format=3
ExprPercentWidth=80

[WCTolerance]
Var Width=100
Nominal Width=72
Tol Width=152
Tol Name=Drift
Col Width Neq=50
Col Width Pos=50
Col Width Rnd=50

[WCFiles]
UseFile=<Library>Standard.tlib
AVAILABLE_FILE=<Library>Standard.tlib

[OPMethods]
Analysis=Transient
Standard Newton-Raphson=0,0
Source Stepping=0,0
Diagonal Gmin Stepping=0,0
Junction Gmin Stepping=0,0
Pseudo Transient=0,0

[OPMethods]
Analysis=AC
Standard Newton-Raphson=0,0
Source Stepping=0,0
Diagonal Gmin Stepping=0,0
Junction Gmin Stepping=0,0
Pseudo Transient=0,0

[OPMethods]
Analysis=DC
Standard Newton-Raphson=0,0
Source Stepping=0,0
Diagonal Gmin Stepping=0,0
Junction Gmin Stepping=0,0
Pseudo Transient=0,0

[OPMethods]
Analysis=HmDistortion
Standard Newton-Raphson=0,0
Source Stepping=0,0
Diagonal Gmin Stepping=0,0
Junction Gmin Stepping=0,0
Pseudo Transient=0,0

[OPMethods]
Analysis=ImDistortion
Standard Newton-Raphson=0,0
Source Stepping=0,0
Diagonal Gmin Stepping=0,0
Junction Gmin Stepping=0,0
Pseudo Transient=0,0

[OPMethods]
Analysis=Stability
Standard Newton-Raphson=0,0
Source Stepping=0,0
Diagonal Gmin Stepping=0,0
Junction Gmin Stepping=0,0
Pseudo Transient=0,0

[OPMethods]
Analysis=DynamicAC
Standard Newton-Raphson=0,0
Source Stepping=0,0
Diagonal Gmin Stepping=0,0
Junction Gmin Stepping=0,0
Pseudo Transient=0,0

[OPMethods]
Analysis=DynamicDC
Standard Newton-Raphson=0,0
Source Stepping=0,0
Diagonal Gmin Stepping=0,0
Junction Gmin Stepping=0,0
Pseudo Transient=0,0
