KaisLissera/IR-motion-sensor/Bagryanets_fw/Inc/rcc_F072.h

/*
 * rcc_F072.h
 *
 *  Created on: 2023.07.31
 *      Author: Kais Lissera
 */

#ifndef INC_RCC_H_
#define INC_RCC_H_

#include <stdint.h>
//
#include <lib.h>

//Simple delays
/////////////////////////////////////////////////////////////////////

//Attention! SysTick delay conflicts with FreeRTOS
#if (USE_SYSTICK_DELAY == 1)
volatile static uint32_t systickCount;
void DelayMs(uint32_t ms);

extern "C"
void SysTick_Handler(void);
#endif

void BlockingDelay(uint32_t ms);

//Functions to setup system clock and peripheral clock control
/////////////////////////////////////////////////////////////////////

//Frequencies of the internal oscillators in Hz
#define HSI8_FREQ_HZ     8000000UL
#define HSI14_FREQ_HZ   14000000UL // Dedicated for ADC
#define HSI48_FREQ_HZ   48000000UL // Primarily for USB
#define LSI_FREQ_HZ     40000UL
#define LSE_FREQ_HZ     32768UL

typedef enum {
	apbDiv1 = 0b000, apbDiv2 = 0b100, apbDiv4 = 0b101, apbDiv8 = 0b110,	apbDiv16 = 0b111
} ApbDiv_t; // PCLK prescaler  - RCC_CFGR_PPRE

typedef enum {
    ahbDiv1		= 0b0000,
    ahbDiv2		= 0b1000,
    ahbDiv4		= 0b1001,
    ahbDiv8		= 0b1010,
    ahbDiv16	= 0b1011,
    ahbDiv64	= 0b1100,
    ahbDiv128	= 0b1101,
    ahbDiv256	= 0b1110,
    ahbDiv512	= 0b1111
} AhbDiv_t; // HCLK prescaler - RCC_CFGR_HPRE

typedef enum {
	sysClkHsi = 0b00,
	sysClkHse = 0b01,
	sysClkPll = 0b10,
	sysClkHsi48 = 0b11
} SysClkSource_t; // System clock switch status

typedef enum {
	pllSrcHsiDiv2 = 0b00,
	pllSrcHsiPrediv = 0b01,
	pllSrcHsePrediv = 0b10,
	pllSrcHsi48Prediv = 0b11
} PllSource_t; // PLL input clock source

namespace rcc {
	void ResetAll();
	void DisableAllClocks();

	uint8_t EnableLSI(uint32_t Timeout = 0xFFF);
	uint8_t EnableHSI8(uint32_t Timeout = 0xFFF);
	uint8_t EnableHSE(uint32_t Timeout = 0xFFF);
	uint8_t EnableHSI14(uint32_t Timeout = 0xFFF);
	uint8_t EnableHSI48(uint32_t Timeout = 0xFFF);
	uint8_t EnablePLL(uint32_t Timeout = 0xFFF);
	// Need to add timeout until RDY bit is cleared !!!!
	inline void DisableLSI() {RCC -> CSR &= ~RCC_CSR_LSION;};
	inline void DisableHSI8() {RCC -> CR &= ~RCC_CR_HSION;};
	inline void DisableHSI14() {RCC -> CR2 &= ~RCC_CR2_HSI14ON;};
	inline void DisableHSI48() {RCC -> CR2 &= ~RCC_CR2_HSI48ON;};
	inline void DisableHSE() {RCC -> CR &= ~RCC_CR_HSEON;};
	inline void DisablePLL() {RCC -> CR &= ~RCC_CR_PLLON;};
	//
	uint8_t SwitchSysClk(SysClkSource_t SysClkSource, uint32_t Timeout = 0xFFF);
	void SetBusDividers(AhbDiv_t AhbDiv, ApbDiv_t ApbDiv);

	// 2 <= pllMul <= 16, 1 <= pllPrediv <= 16
	uint8_t SetupPLL(PllSource_t pllSrc, uint32_t pllMul, uint32_t pllPrediv);
	//
	uint32_t GetCurrentSystemClock();
	uint32_t GetCurrentAHBClock(uint32_t currentSystemClockHz);
	uint32_t GetCurrentAPBClock(uint32_t currentAhbClockHz);
	uint32_t GetCurrentTimersClock(uint32_t currentApbClockHz);

	//Functions to enable peripheral clocks
	//AHB
	inline void EnableClkAHB(uint32_t ahbPeripheral) {RCC->AHBENR |= ahbPeripheral;}
	inline void DisableClkAHB(uint32_t ahbPeripheral) {RCC->AHBENR &= ~ahbPeripheral;}

	//APB1
	inline void EnableClkAPB1(uint32_t apb1Peripheral) {RCC->APB1ENR |= apb1Peripheral;}
	inline void DisableClkAPB1(uint32_t apb1Peripheral) {RCC->APB1ENR &= ~apb1Peripheral;}

	//APB1
	inline void EnableClkAPB2(uint32_t apb2Peripheral) {RCC->APB2ENR |= apb2Peripheral;}
	inline void DisableClkAPB2(uint32_t apb2Peripheral) {RCC->APB2ENR &= ~apb2Peripheral;}
};//rcc end

//Sleep and low power modes
/////////////////////////////////////////////////////////////////////

namespace power {
	// If wakeup enabled pin forced low, WKUP on rising edge
	// PA0
	inline void EnableWakeup1(void) {PWR->CSR |= PWR_CSR_EWUP1;}
	// PC13
	inline void EnableWakeup2(void) {PWR->CSR |= PWR_CSR_EWUP2;}
	// PE6
	inline void EnableWakeup3(void) {PWR->CSR |= PWR_CSR_EWUP3;}
	// PA2
	inline void EnableWakeup4(void) {PWR->CSR |= PWR_CSR_EWUP4;}
	// PC5
	inline void EnableWakeup5(void) {PWR->CSR |= PWR_CSR_EWUP5;}
	// PB5
	inline void EnableWakeup6(void) {PWR->CSR |= PWR_CSR_EWUP6;}
	// PB15
	inline void EnableWakeup7(void) {PWR->CSR |= PWR_CSR_EWUP7;}

	inline void EnterSleep() { // Core clock disabled, all peripherals running
		PWR->CR = PWR_CR_CWUF | PWR_CR_CSBF; //Clear wakeup flags
		SCB->SCR &= ~SCB_SCR_SLEEPDEEP_Msk;
		__WFI();
	} // Wake-up - interrupt/wake-up event

	inline void EnterStop() { // All clocks are stopped
		PWR->CR = PWR_CR_CWUF | PWR_CR_CSBF; //Clear wakeup flags
		PWR->CR &= ~PWR_CR_PDDS;
		PWR->CR |= PWR_CR_LPDS;
		SCB->SCR |= SCB_SCR_SLEEPDEEP_Msk;
		__WFI();
	} // Wake-up - EXTI line

	inline void EnterStandby() { // VDD domain povwered-off
		PWR->CR = PWR_CR_CWUF | PWR_CR_CSBF; //Clear wakeup flags
		PWR->CR |= PWR_CR_PDDS;
		PWR->CR |= PWR_CR_LPDS;
		SCB->SCR |= SCB_SCR_SLEEPDEEP_Msk;
	    __WFI();
	} // Wake-up - WKUP pin, RTC, NRST, IWDG
};

//FLASH setup
/////////////////////////////////////////////////////////////////////

namespace flash {
	void SetFlashLatency(uint8_t AhbClkMHz);
}

//NVIC setup
/////////////////////////////////////////////////////////////////////

namespace nvic {
	inline void SetupIrq(IRQn_Type IRQ, uint8_t Priority) {
		NVIC_EnableIRQ(IRQ);
		NVIC_SetPriority(IRQ, Priority);
	}
}

#endif /* INC_RCC_H_ */
